czagrzebski/AMC13XM0X-Module/documentation/image-2.png

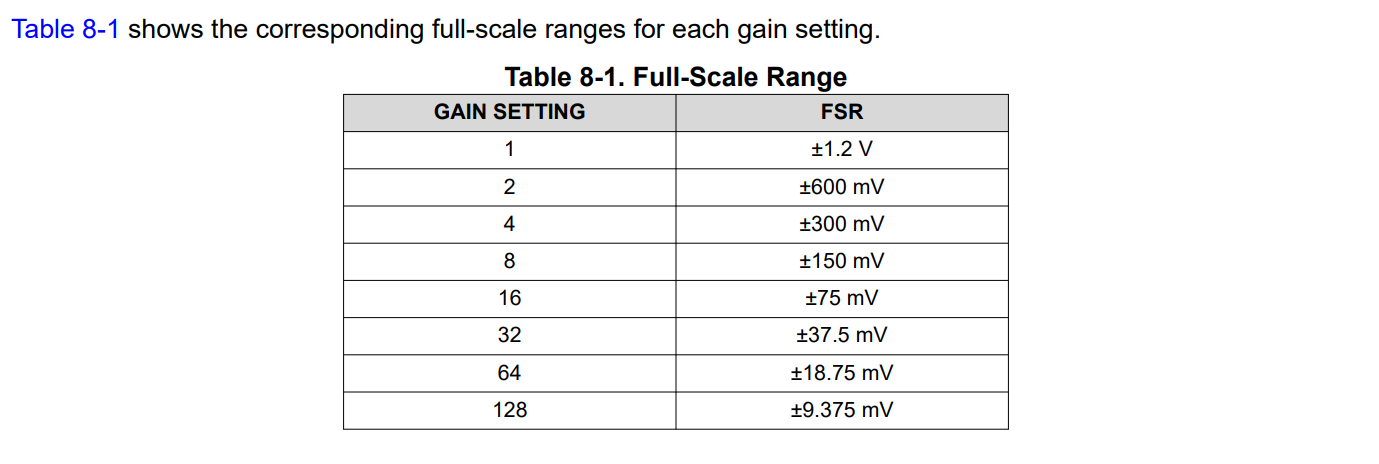
documentation/image-2.png
